JavierGarSan/EConversn/Electrical Ciruit/ebikePCB_etch_silk_bottom.pdf

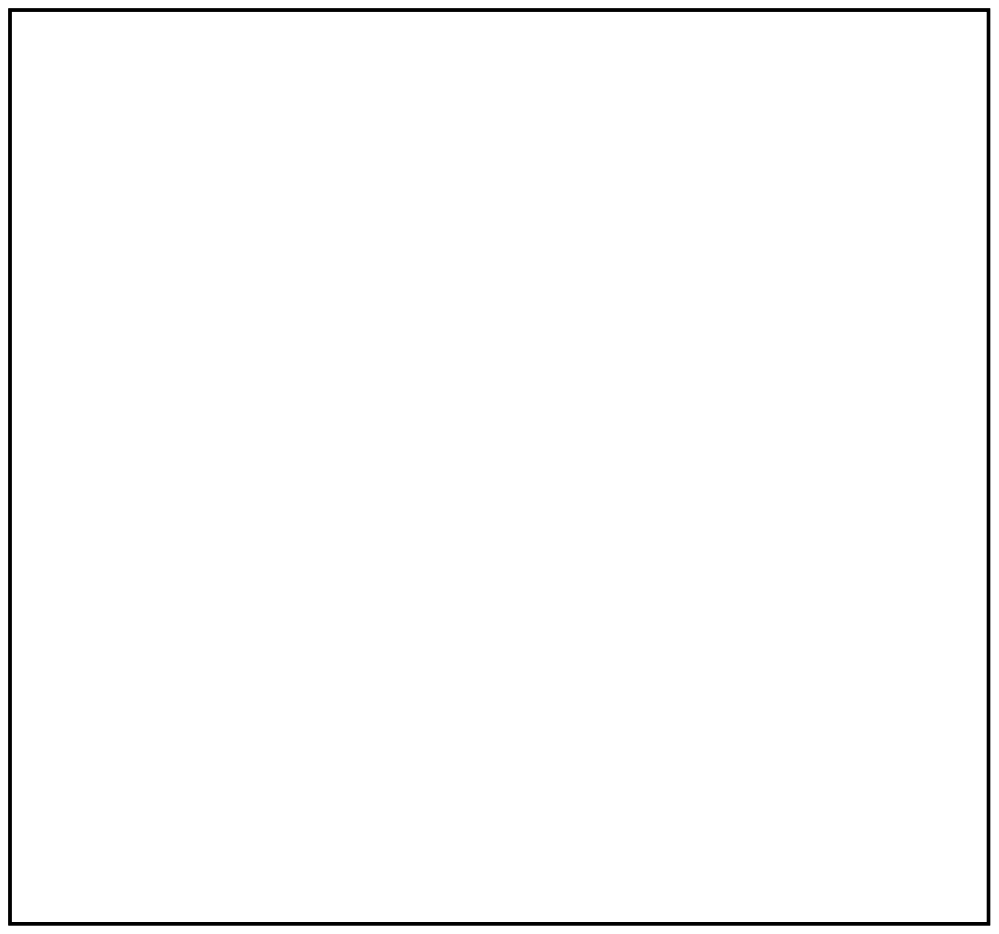
[picture p17: page 1]
