JavierGarSan/EConversn/Electrical Ciruit/ebikePCB_etch_silk_bottom_mirror.pdf

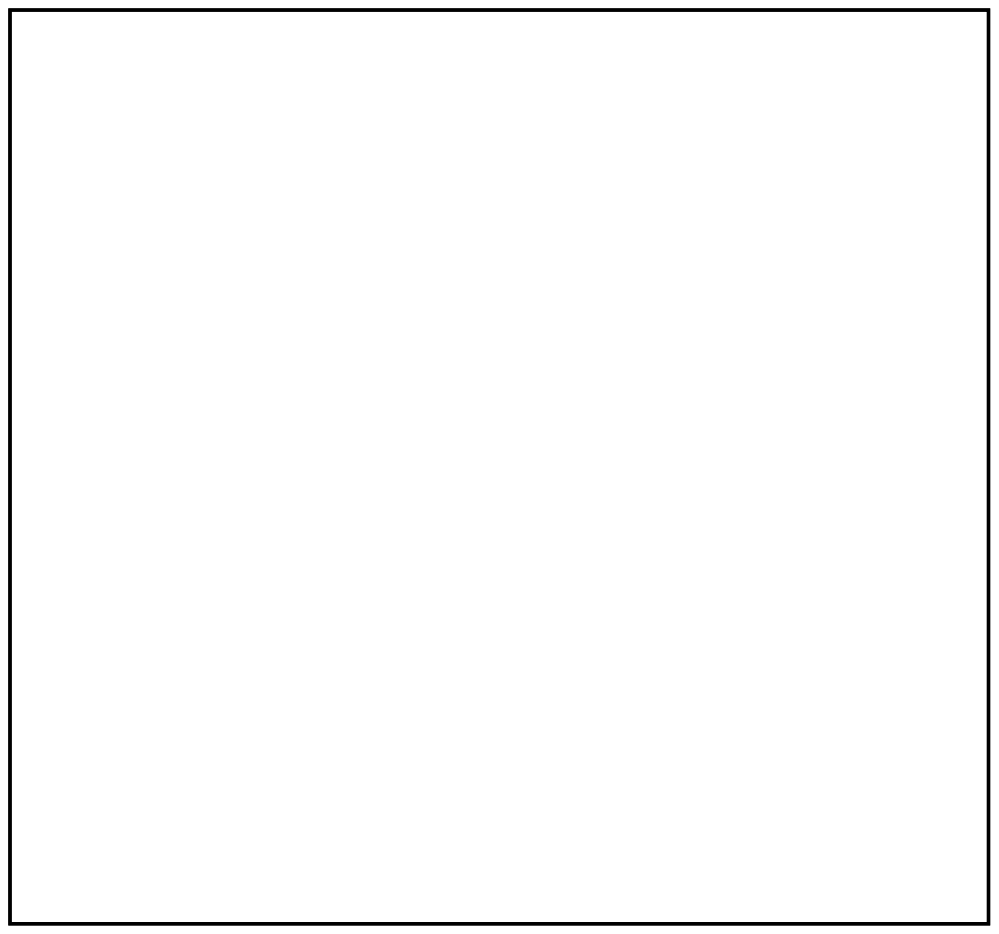
[picture p18: page 1]
