JavierGarSan/EConversn/Electrical Ciruit/ebikePCB_etch_silk_top.pdf

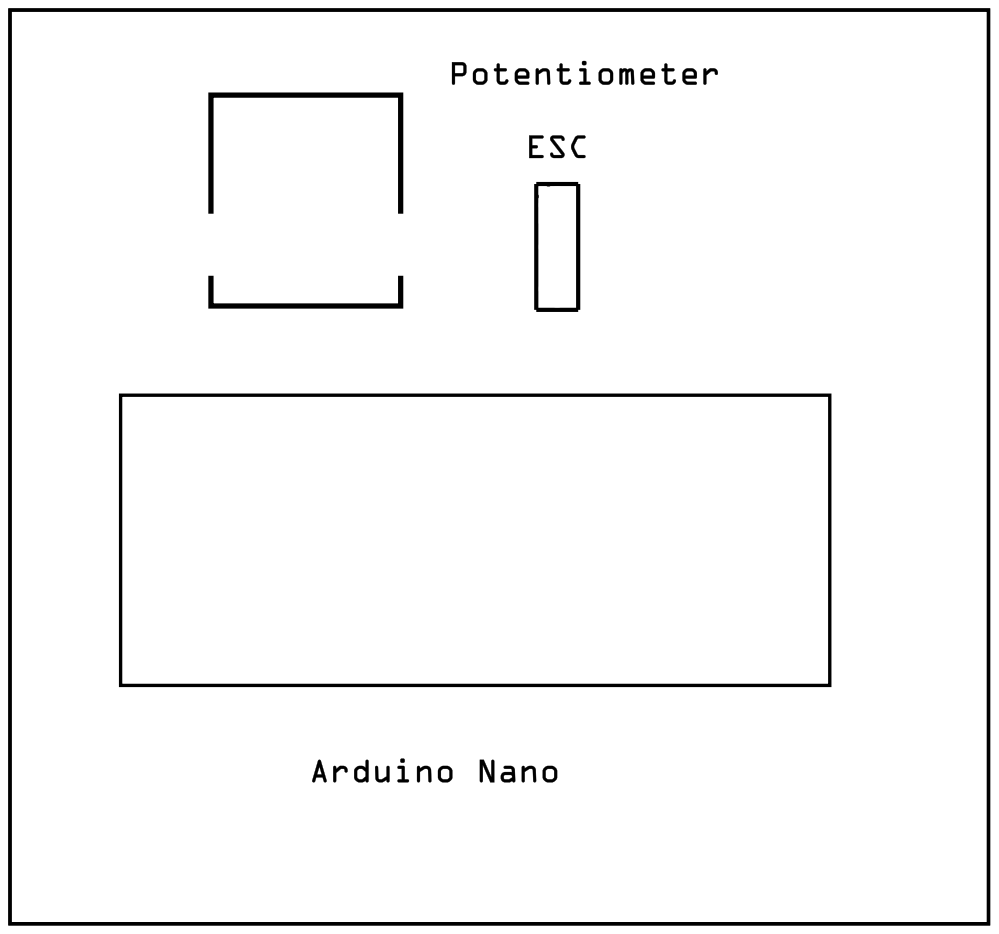
[picture p19: page 1]
