JavierGarSan/EConversn/Electrical Ciruit/ebikePCB_etch_silk_top_mirror.pdf

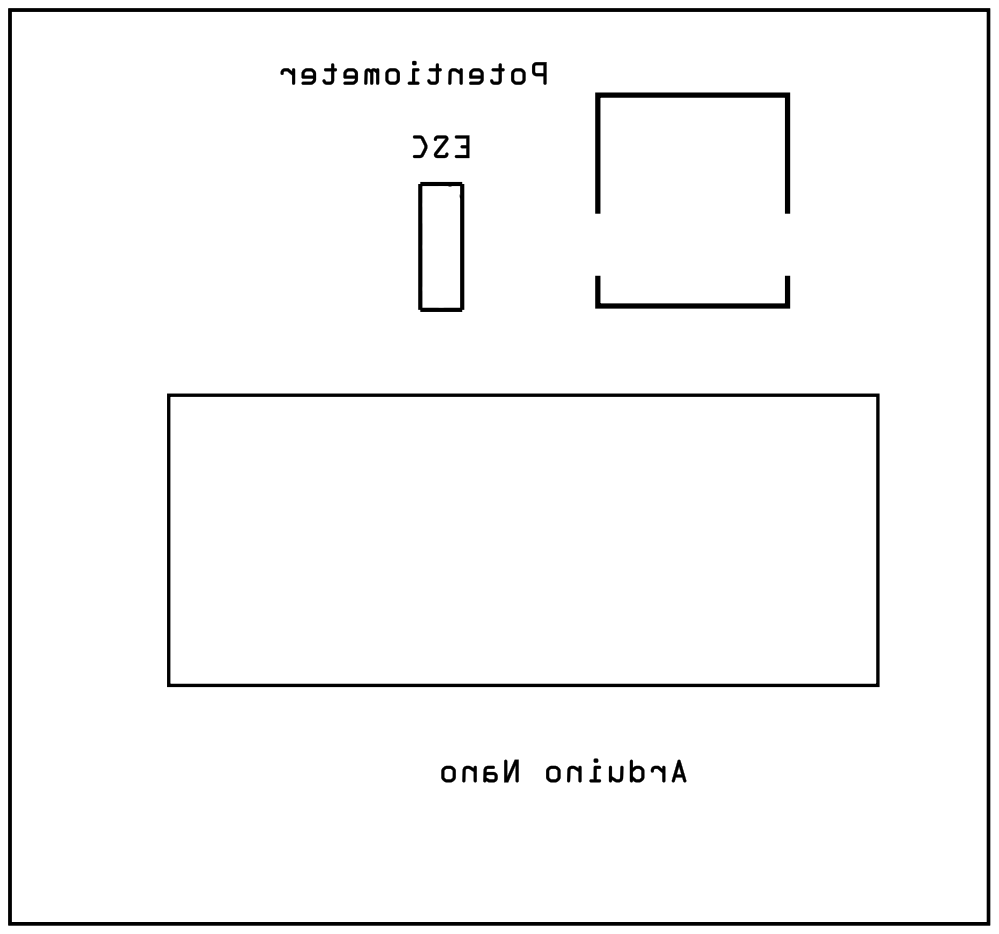
[picture p20: page 1]
